Jajaho/Bosch-Dremel-GAL-1215-CV-repair/battery/battery_pcb_underside.jpg

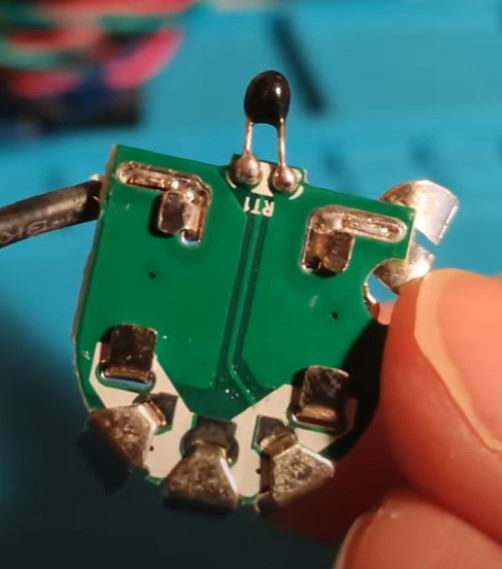
battery/battery_pcb_underside.jpg
