Jajaho/Bosch-Dremel-GAL-1215-CV-repair/reverse engineering/IMG_20230427_183510.jpg

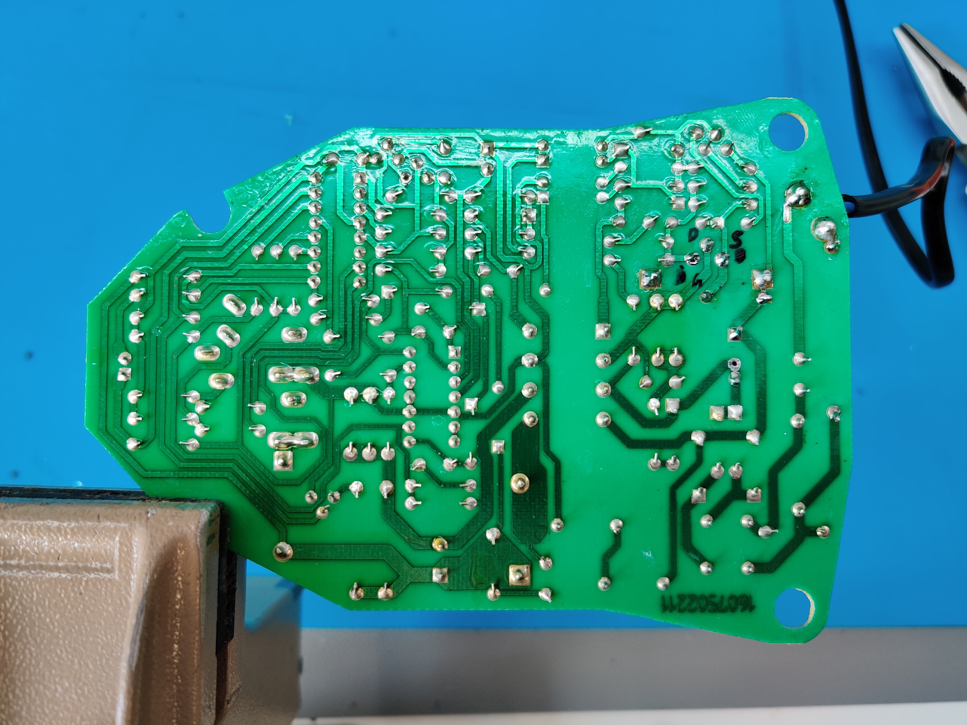
reverse engineering/IMG_20230427_183510.jpg
