Jajaho/Bosch-Dremel-GAL-1215-CV-repair/reverse engineering/IMG_20230427_183529.jpg

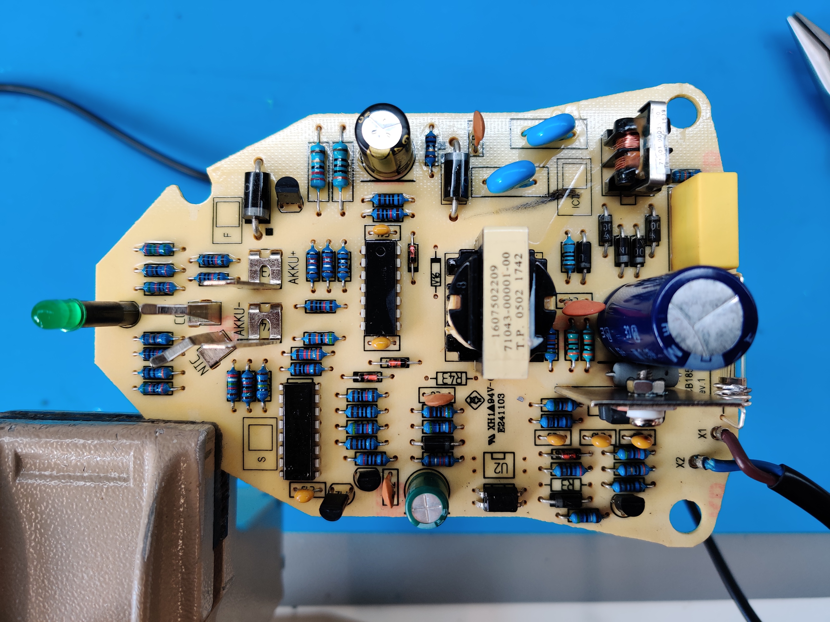
reverse engineering/IMG_20230427_183529.jpg
